SolentAirWatch/buildPlans/images/6.jpg

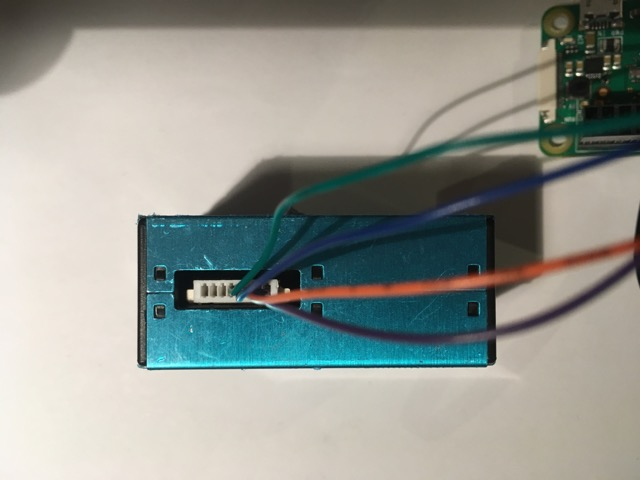
images/6.jpg
